Kotoubiyca/MacroPad_BLE_ESP32-C3-SuperMini/src/debug.hpp

#pragma once

// 0 = serial print debug logs on, 1 = serial print debug logs off
#define DEBUG_ENABLED 0

#if DEBUG_ENABLED
  #define DBG(x) Serial.print(x)
  #define DBGLN(x) Serial.println(x)
  #define DBGF(...) Serial.printf(__VA_ARGS__)
#else
  #define DBG(x)
  #define DBGLN(x)
  #define DBGF(...)
#endif
